brgerig/Magic-Clock/ClockPrimary-HA/config.h

#define SSID                          "WiFiSSID"
#define PASSWORD                      "WiFiPWD"

// MQTT Settings
#define HOSTNAME                      "magic-clock"
#define MQTT_SERVER                   "something.cloudmqtt.com"
#define MQTT_PORT                     11111
#define MQTT_USER                     "clockuser"
#define MQTT_PASS                     "clockpass"
